HelenaMaslowska/Minecraft-box/Box photos/1670782595009.jpg

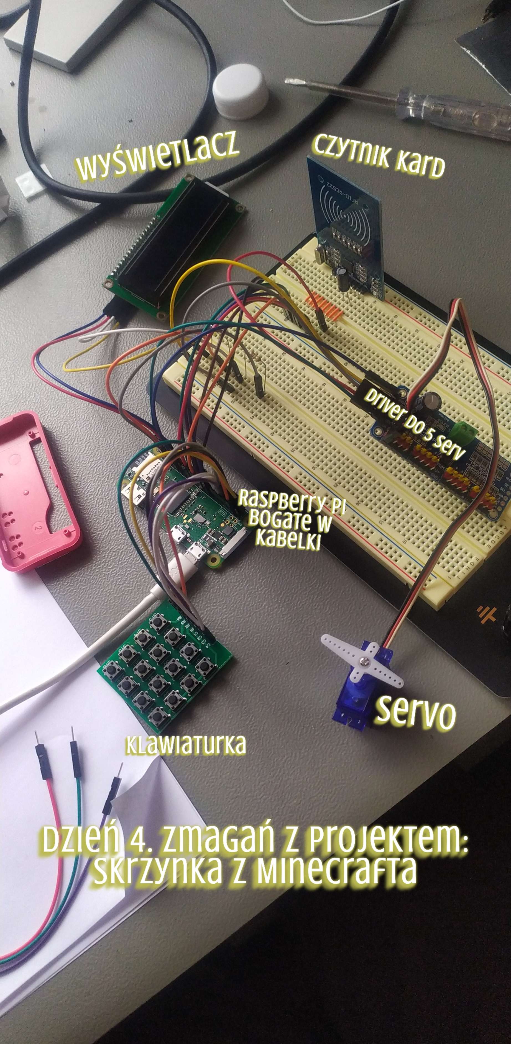
Box photos/1670782595009.jpg
