HelenaMaslowska/Minecraft-box/Box photos/1670796617963.jpg

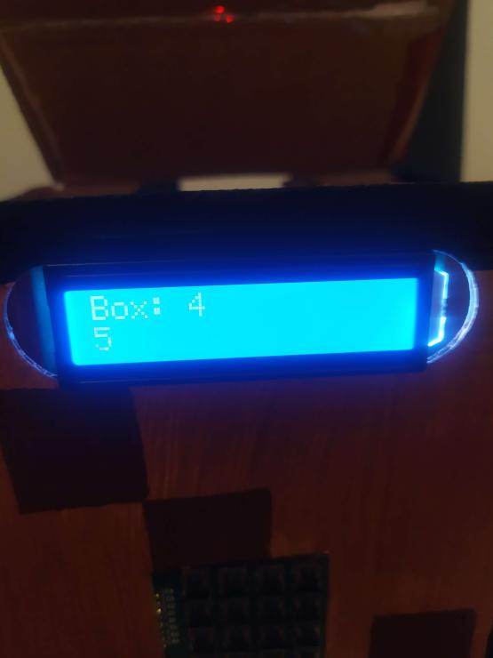
Box photos/1670796617963.jpg
